Abhishekjha18/SONAR-AND-TRANSFORMER/2022023_1.asc

D1: diode
R1: res; 100
V1: voltage; SINE(0 15 50)
Named nets: 0
.dc V1 0 15 0.01
