Abhishekjha18/SONAR-AND-TRANSFORMER/2022023_2.asc

D1: diode
R1: res; 3300
V1: voltage; 15
Named nets: 0
.dc V1 0 15 0.1
