Abhishekjha18/SONAR-AND-TRANSFORMER/2022023_3.asc

D1: diode
D2: diode
D3: diode
D4: diode
R1: res; 1
V1: voltage; SINE(0 15 50)
