Abhishekjha18/SONAR-AND-TRANSFORMER/lab2_abhishek_ctd.asc

G1: g; 1
G2: g; {1/N}
G3: g; 1
G4: g; {1/N}
R1: res; 50
R2: res; 1G
R3: res; 100
V1: voltage; SINE(0 350 50)
Named nets: 0
.tran 0.1s
This example schematic is supplied for informational/educational purposes only.
A ideal transformer with two windings.
Winding ratio specified with parameter N
.param N=1/15 ; turns ratio
