Abhishekjha18/SONAR-AND-TRANSFORMER/lab5.asc

D1: zener; 1N750
R1: res; 1000
R2: res; 100
V1: voltage; 15
.model 1N750 D(Is=1.004f Rs=.5875 Ikf=0 N=1 Xti=3
Eg=1.11 Cjo=160p M=.5484 Vj=.75 Fc=.5 Isr=1.8n
Nr=2 Bv=5.1 Ibv=27.721m Nbv=1.1779
Ibvl=1.1646m Nbvl=21.894 Tbv1=176.47u Vpk=5.1
mfg=Motorola type=zener)
.tran 0.1
