Abhishekjha18/SONAR-AND-TRANSFORMER/LCF_2022023.asc

C1: cap; 100n
L1: ind; 10µ
R1: res; 100
V1: voltage; ""; AC 1
Named nets: 0
LC_FILTER
