Abhishekjha18/SONAR-AND-TRANSFORMER/Series_Indc_Filter_2022023.asc

L1: ind; 10m
R1: res; 100
V1: voltage; ""; AC 1
Named nets: 0
