Abhishekjha18/SONAR-AND-TRANSFORMER/Shunt_Capa_Filter_2022023.asc

C1: cap; 10µ
R1: res; 100
V1: voltage; ""; AC 1
Named nets: 0
SHUNT CAP FILTER
